NeusAap/ShotClock/hw/ShotClockProject/output/img/Screenshot_20230716_172328.png

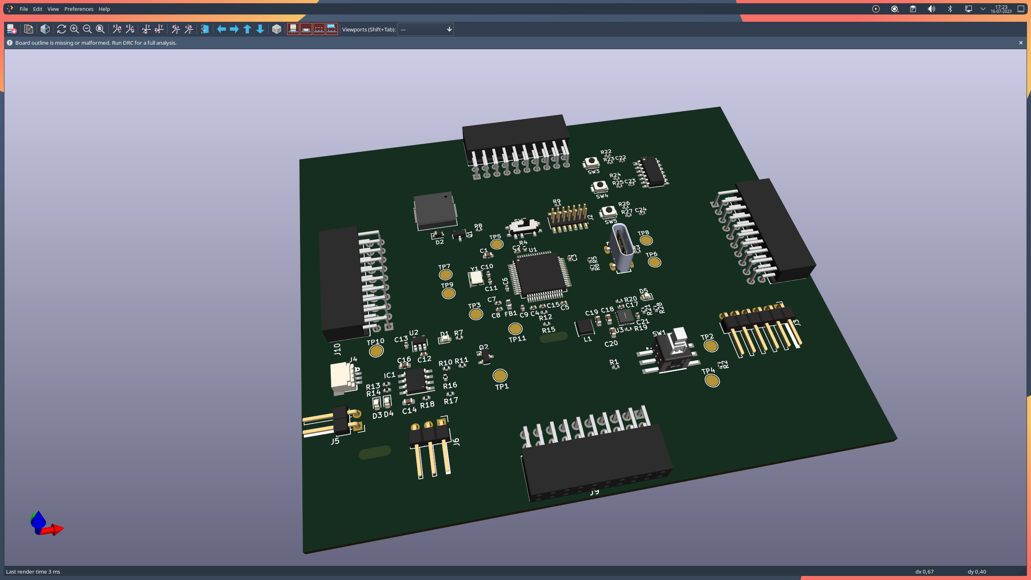
hw/ShotClockProject/output/img/Screenshot_20230716_172328.png
