NeusAap/ShotClock/sw/firmware/Core/Src/adc.c

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
/* Includes ------------------------------------------------------------------*/
#include "adc.h"

ADC_HandleTypeDef hadc1;

/* ADC1 init function */
void MX_ADC1_Init(void)
{

  ADC_ChannelConfTypeDef sConfig = {0};

  /** Configure the global features of the ADC (Clock, Resolution, Data Alignment and number of conversion)
  */
  hadc1.Instance = ADC1;
  hadc1.Init.ClockPrescaler = ADC_CLOCK_ASYNC_DIV1;
  hadc1.Init.Resolution = ADC_RESOLUTION_12B;
  hadc1.Init.DataAlign = ADC_DATAALIGN_RIGHT;
  hadc1.Init.ScanConvMode = ADC_SCAN_DISABLE;
  hadc1.Init.EOCSelection = ADC_EOC_SINGLE_CONV;
  hadc1.Init.LowPowerAutoWait = DISABLE;
  hadc1.Init.LowPowerAutoPowerOff = DISABLE;
  hadc1.Init.ContinuousConvMode = DISABLE;
  hadc1.Init.NbrOfConversion = 1;
  hadc1.Init.DiscontinuousConvMode = DISABLE;
  hadc1.Init.ExternalTrigConv = ADC_SOFTWARE_START;
  hadc1.Init.ExternalTrigConvEdge = ADC_EXTERNALTRIGCONVEDGE_NONE;
  hadc1.Init.DMAContinuousRequests = DISABLE;
  hadc1.Init.Overrun = ADC_OVR_DATA_PRESERVED;
  hadc1.Init.SamplingTimeCommon1 = ADC_SAMPLETIME_39CYCLES_5;
  hadc1.Init.SamplingTimeCommon2 = ADC_SAMPLETIME_39CYCLES_5;
  hadc1.Init.OversamplingMode = DISABLE;
  hadc1.Init.TriggerFrequencyMode = ADC_TRIGGER_FREQ_HIGH;
  if (HAL_ADC_Init(&hadc1) != HAL_OK)
  {
    Error_Handler();
  }

  /** Configure Regular Channel
  */
  sConfig.Channel = ADC_CHANNEL_0;
  sConfig.Rank = ADC_REGULAR_RANK_1;
  sConfig.SamplingTime = ADC_SAMPLINGTIME_COMMON_1;
  if (HAL_ADC_ConfigChannel(&hadc1, &sConfig) != HAL_OK)
  {
    Error_Handler();
  }
}

void HAL_ADC_MspInit(ADC_HandleTypeDef* adcHandle)
{

  GPIO_InitTypeDef GPIO_InitStruct = {0};
  RCC_PeriphCLKInitTypeDef PeriphClkInit = {0};
  if(adcHandle->Instance==ADC1)
  {
  /** Initializes the peripherals clocks
  */
    PeriphClkInit.PeriphClockSelection = RCC_PERIPHCLK_ADC;
    PeriphClkInit.AdcClockSelection = RCC_ADCCLKSOURCE_SYSCLK;
    if (HAL_RCCEx_PeriphCLKConfig(&PeriphClkInit) != HAL_OK)
    {
      Error_Handler();
    }

    /* ADC1 clock enable */
    __HAL_RCC_ADC_CLK_ENABLE();

    __HAL_RCC_GPIOA_CLK_ENABLE();
    /**ADC1 GPIO Configuration
    PA0     ------> ADC1_IN0
    */
    GPIO_InitStruct.Pin = ADC_BATT_IN_Pin;
    GPIO_InitStruct.Mode = GPIO_MODE_ANALOG;
    GPIO_InitStruct.Pull = GPIO_NOPULL;
    HAL_GPIO_Init(ADC_BATT_IN_GPIO_Port, &GPIO_InitStruct);

  }
}

void HAL_ADC_MspDeInit(ADC_HandleTypeDef* adcHandle)
{

  if(adcHandle->Instance==ADC1)
  {
    /* Peripheral clock disable */
    __HAL_RCC_ADC_CLK_DISABLE();

    /**ADC1 GPIO Configuration
    PA0     ------> ADC1_IN0
    */
    HAL_GPIO_DeInit(ADC_BATT_IN_GPIO_Port, ADC_BATT_IN_Pin);

  }
}

/* USER CODE BEGIN 1 */
uint16_t adc_value;
float sampled_voltage = 0.0f;
float battery_correction_factor = 0.9497206703910615f;

// Function to read ADC value and convert to voltage
void SampleBatteryVoltage() {
    // Start ADC conversion
    if (HAL_ADC_Start(&hadc1) != HAL_OK) {
        Error_Handler();
    }
    // Wait for ADC conversion to complete
    HAL_ADC_PollForConversion(&hadc1, HAL_MAX_DELAY);
    // Read ADC value
    adc_value = HAL_ADC_GetValue(&hadc1);
    // Convert ADC value to voltage (assuming VREF is 3.3V and ADC is 12-bit)
    sampled_voltage = ((float)adc_value / 4095 * 3.3) * 2 * battery_correction_factor;
    // HAL_Delay(10);
}

// Function to get the sampled voltage
float GetBatteryVoltage() {
    return sampled_voltage;
}
/* USER CODE END 1 */
